deckerego/vending_machine/docs/Mark II/images/sizing_dowel_mount.png

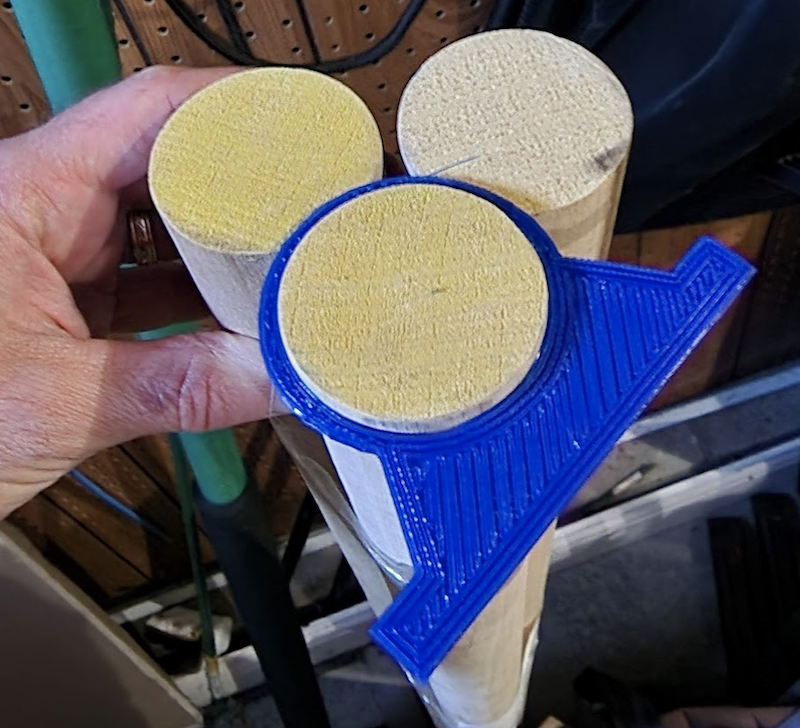
docs/Mark II/images/sizing_dowel_mount.png
